Jana-Marie/OtterPill/images/2_3.jpg

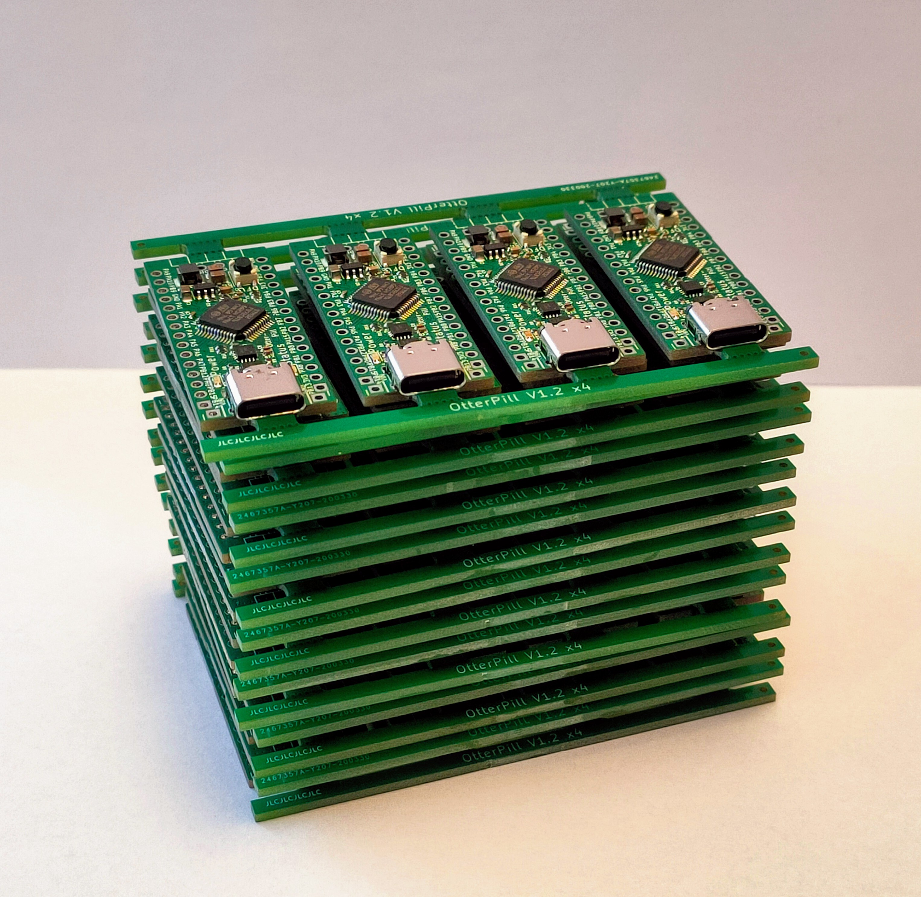
images/2_3.jpg
