Jana-Marie/OtterPill/HW vG1.0/test/Inc/usbpd_pdo_defs.h

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

#ifndef __USBPD_PDO_DEF_H_
#define __USBPD_PDO_DEF_H_

#ifdef __cplusplus
 extern "C" {
#endif 

/* Includes ------------------------------------------------------------------*/
#include "main.h"
#include "usbpd_def.h"

/* Define   ------------------------------------------------------------------*/
#define PORT0_NB_SOURCEPDO         0U   /* Number of Source PDOs (applicable for port 0)   */
#define PORT0_NB_SINKPDO           1U   /* Number of Sink PDOs (applicable for port 0)     */
#define PORT1_NB_SOURCEPDO         0U   /* Number of Source PDOs (applicable for port 1)   */
#define PORT1_NB_SINKPDO           0U   /* Number of Sink PDOs (applicable for port 1)     */

/* Exported typedef ----------------------------------------------------------*/

/* USER CODE BEGIN typedef */

/**
  * @brief  USBPD Port PDO Structure definition
  *
  */

/* USER CODE END typedef */

/* Exported define -----------------------------------------------------------*/

/* USER CODE BEGIN Exported_Define */

#define USBPD_CORE_PDO_SRC_FIXED_MAX_CURRENT 3
#define USBPD_CORE_PDO_SNK_FIXED_MAX_CURRENT 1500

/* USER CODE END Exported_Define */

/* Exported constants --------------------------------------------------------*/

/* Exported macro ------------------------------------------------------------*/

/* Exported variables --------------------------------------------------------*/

#ifndef __USBPD_PWR_IF_C
extern uint8_t USBPD_NbPDO[4];
extern uint32_t PORT0_PDO_ListSRC[USBPD_MAX_NB_PDO];
extern uint32_t PORT0_PDO_ListSNK[USBPD_MAX_NB_PDO];
#else
uint8_t USBPD_NbPDO[4] = {(PORT0_NB_SINKPDO),
                          (PORT0_NB_SOURCEPDO)};
/* Definition of Source PDO for Port 0 */
uint32_t PORT0_PDO_ListSRC[USBPD_MAX_NB_PDO] =
{
  /* PDO 1 */
        (0x00000000U),
  /* PDO 2 */
        (0x00000000U),
  /* PDO 3 */
        (0x00000000U),
  /* PDO 4 */
        (0x00000000U),
  /* PDO 5 */
        (0x00000000U),
  /* PDO 6 */
        (0x00000000U),
  /* PDO 7 */
        (0x00000000U)
};

/* Definition of Sink PDO for Port 0 */
uint32_t PORT0_PDO_ListSNK[USBPD_MAX_NB_PDO] =
{
  /* PDO 1 */
        (0x26019096U),
  /* PDO 2 */
        (0x00000000U),
  /* PDO 3 */
        (0x00000000U),
  /* PDO 4 */
        (0x00000000U),
  /* PDO 5 */
        (0x00000000U),
  /* PDO 6 */
        (0x00000000U),
  /* PDO 7 */
        (0x00000000U)
};

#endif

/* Exported functions --------------------------------------------------------*/

#ifdef __cplusplus
}
#endif

#endif /* __USBPD_PDO_DEF_H_ */

/************************ (C) COPYRIGHT STMicroelectronics *****END OF FILE****/
