Jana-Marie/OtterPill/HW vG1.0/test/Inc/usbpd_gui_memmap.h

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

#ifndef __USBPD_GUI_MEMMAP_H_
#define __USBPD_GUI_MEMMAP_H_

#ifdef __cplusplus
 extern "C" {
#endif

/* Includes ------------------------------------------------------------------*/
#include "stm32g0xx.h"
#include "usbpd_def.h"

/** @addtogroup STM32_USBPD_APPLICATION
  * @{
  */

/** @addtogroup STM32_USBPD_APPLICATION_GUI
  * @{
  */

/* Exported typedef ----------------------------------------------------------*/

/* Exported define -----------------------------------------------------------*/

/* Following definitions should be adapted to used Flash configuration :
   INDEX_PAGE : represents the number of the page used for storing USBPD settings (usually the last page)
   ADDR_FLASH_LAST_PAGE : Flash address value of begining of USBPD settings page
   ADDR_FLASH_PAGE_END : Flash address value of end of USBPD settings page
*/

#if defined (FLASH_OPTR_DBANK)
#define INDEX_PAGE              ((FLASH_PAGE_NB * 2u) - 1u)          /* Index of latest page    */
#else
#define INDEX_PAGE              (FLASH_PAGE_NB - 1u)                 /* Index of latest page    */
#endif /* FLASH_OPTR_DBANK */
#define ADDR_FLASH_LAST_PAGE    (FLASH_BASE + (INDEX_PAGE * FLASH_PAGE_SIZE))  /* Base @ of latest page */
#define ADDR_FLASH_PAGE_END     (ADDR_FLASH_LAST_PAGE + FLASH_PAGE_SIZE - 1)

#define GUI_FLASH_ADDR_NB_PDO_SNK_P0  (ADDR_FLASH_LAST_PAGE)
#define GUI_FLASH_ADDR_NB_PDO_SRC_P0  (ADDR_FLASH_LAST_PAGE + 1U)
#define GUI_FLASH_ADDR_NB_PDO_SNK_P1  (ADDR_FLASH_LAST_PAGE + 2U)
#define GUI_FLASH_ADDR_NB_PDO_SRC_P1  (ADDR_FLASH_LAST_PAGE + 3U)

#define GUI_FLASH_ADDR_PDO_SRC_P0      (ADDR_FLASH_LAST_PAGE + 8U)
/* New Address should be modulo 8 */
/* New Address = (Previous Address + (size / 8 * 8) + ((size % 8) + 7) / 8 * 8) */
#define GUI_FLASH_ADDR_PDO_SNK_P0      (GUI_FLASH_ADDR_PDO_SRC_P0 + ((USBPD_MAX_NB_PDO * 4) / 8 * 8) + ((((USBPD_MAX_NB_PDO * 4) & 0x07) + 7) / 8 * 8 ))
#define GUI_FLASH_ADDR_PDO_SRC_P1      (GUI_FLASH_ADDR_PDO_SNK_P0 + ((USBPD_MAX_NB_PDO * 4) / 8 * 8) + ((((USBPD_MAX_NB_PDO * 4) & 0x07) + 7) / 8 * 8 ))
#define GUI_FLASH_ADDR_PDO_SNK_P1      (GUI_FLASH_ADDR_PDO_SRC_P1 + ((USBPD_MAX_NB_PDO * 4) / 8 * 8) + ((((USBPD_MAX_NB_PDO * 4) & 0x07) + 7) / 8 * 8 ))

#define GUI_FLASH_ADDR_DPM_SETTINGS    (GUI_FLASH_ADDR_PDO_SNK_P1 + ((USBPD_MAX_NB_PDO * 4) / 8 * 8) + ((((USBPD_MAX_NB_PDO * 4) & 0x07) + 7) / 8 * 8 ))

/* Define by default USBPD_PORT_COUNT to 2 */
#define GUI_FLASH_ADDR_DPM_USER_SETTINGS  (GUI_FLASH_ADDR_DPM_SETTINGS + (sizeof(USBPD_SettingsTypeDef) * 2 /*USBPD_PORT_COUNT*/))

#define GUI_FLASH_ADDR_DPM_VDM_SETTINGS   (GUI_FLASH_ADDR_DPM_USER_SETTINGS + (sizeof(USBPD_USER_SettingsTypeDef) * 2 /*USBPD_PORT_COUNT*/))

#define GUI_FLASH_ADDR_DPM_ID_SETTINGS    (GUI_FLASH_ADDR_DPM_VDM_SETTINGS + (sizeof(USBPD_VDM_SettingsTypeDef) * 2 /*USBPD_PORT_COUNT*/))

#define GUI_FLASH_ADDR_RESERVED           (GUI_FLASH_ADDR_DPM_ID_SETTINGS + (sizeof(USBPD_IdSettingsTypeDef) * 2 /*USBPD_PORT_COUNT*/))

#define GUI_FLASH_SIZE_RESERVED           (ADDR_FLASH_PAGE_END - GUI_FLASH_ADDR_RESERVED)

/* Exported constants --------------------------------------------------------*/
/* Exported macro ------------------------------------------------------------*/
/* Exported variables --------------------------------------------------------*/

/* Exported functions --------------------------------------------------------*/
/**
  * @}
  */

/**
  * @}
  */

#ifdef __cplusplus
}
#endif

#endif /* __USBPD_GUI_MEMMAP_H_ */

/************************ (C) COPYRIGHT STMicroelectronics *****END OF FILE****/
